brightsole/3d-computer-case/photos/gpu-block-issue.jpg

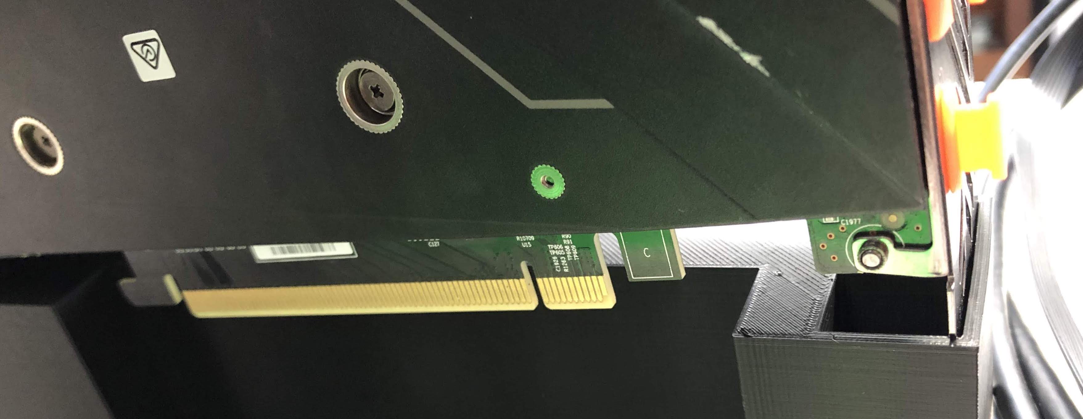
photos/gpu-block-issue.jpg
