brightsole/3d-computer-case/photos/mobo-block-cowling-support-height-issue.jpg

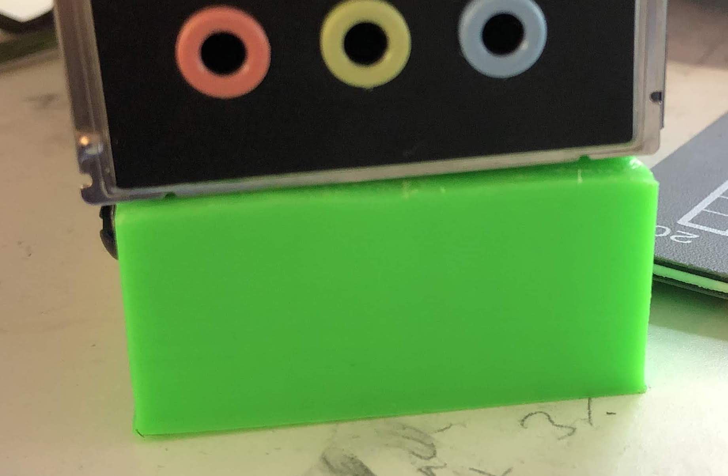
photos/mobo-block-cowling-support-height-issue.jpg
