brightsole/3d-computer-case/photos/mobo-block-height-and-screw-issue.jpg

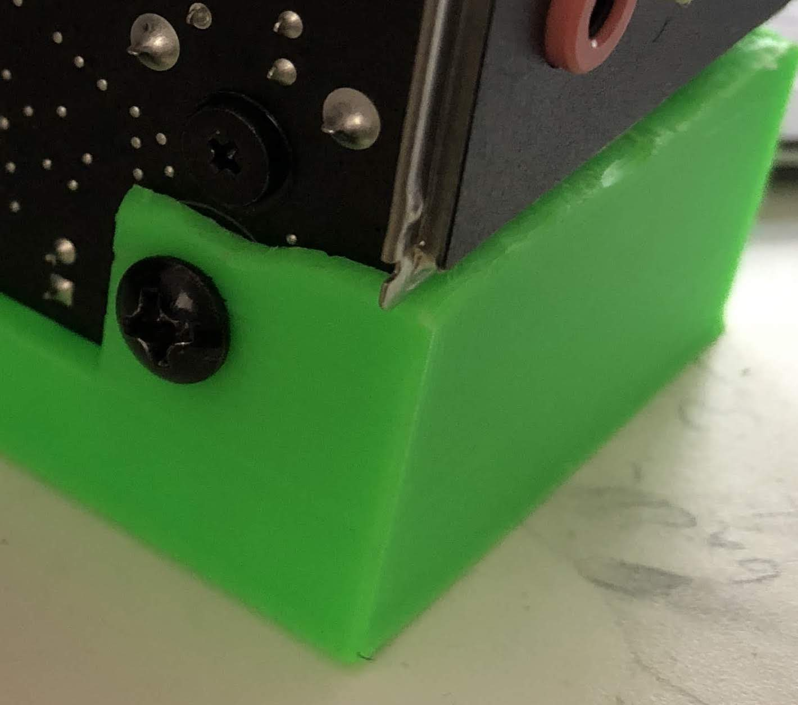
photos/mobo-block-height-and-screw-issue.jpg
