brightsole/3d-computer-case/photos/mobo-block-screw-issue.jpg

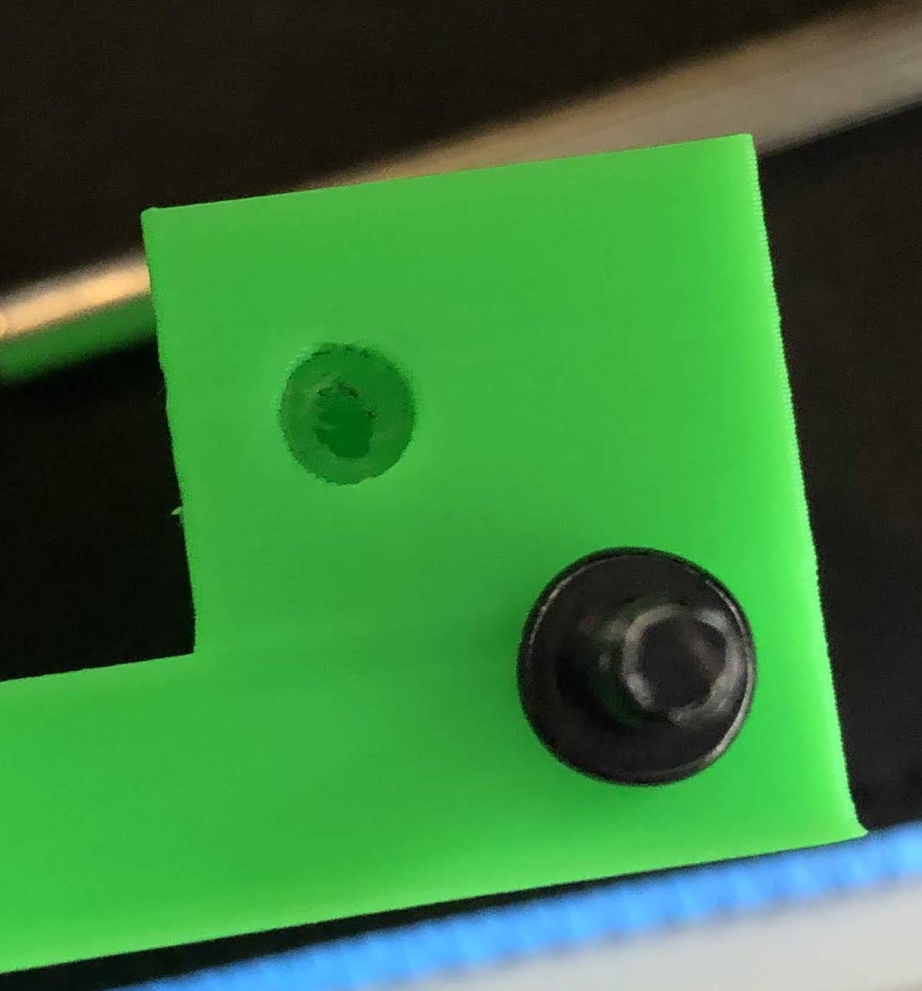
photos/mobo-block-screw-issue.jpg
