brightsole/3d-computer-case/photos/mobo-block-width-issues.jpg

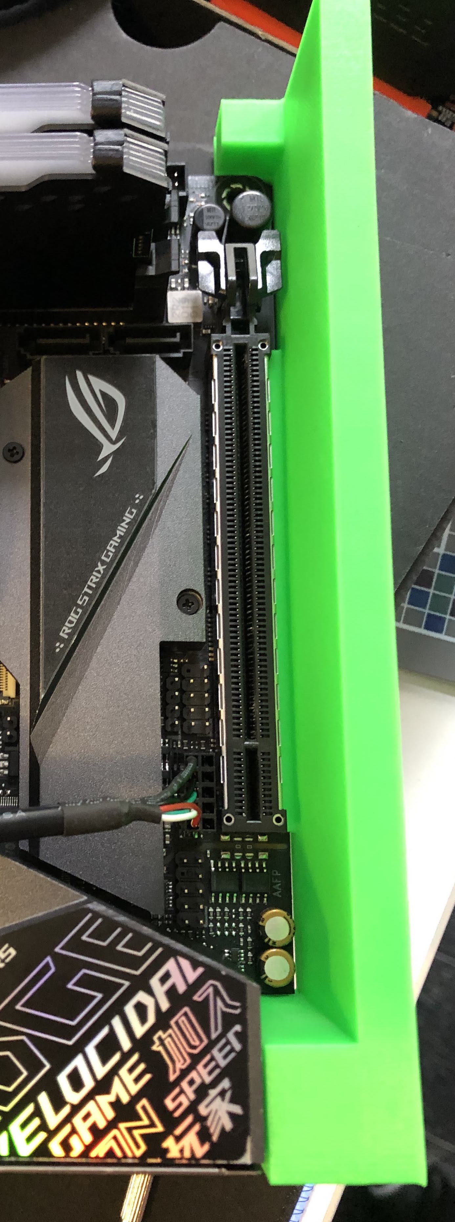
photos/mobo-block-width-issues.jpg
